Beran58/Ozodraha/ozodraha/ozodraha/tileImages/tile_cross.png

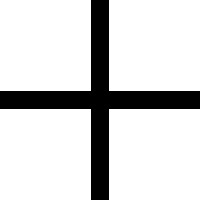
ozodraha/ozodraha/tileImages/tile_cross.png
