Beran58/Ozodraha/ozodraha/ozodraha/tileImages/tile_t_cross.png

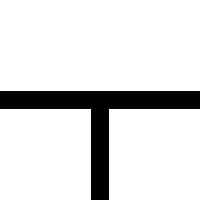
ozodraha/ozodraha/tileImages/tile_t_cross.png
