Beran58/Ozodraha/ozodraha_models/latest_models/slave_module/ozo_platform_v12_bottom.SLDPRT

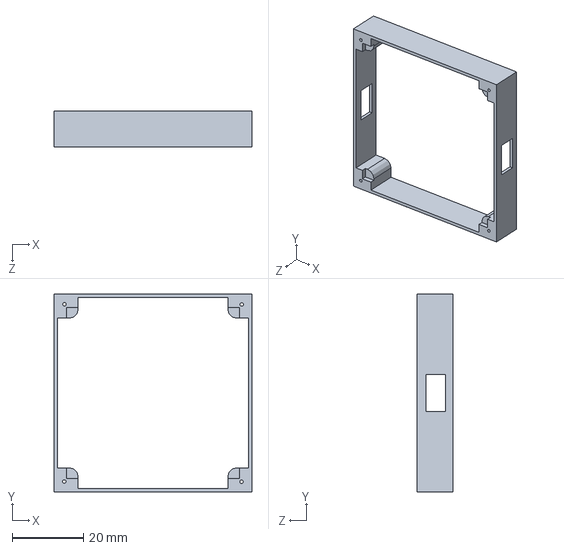
[picture p32: CAD file, 2023-03-25]
ozodraha_models/latest_models/slave_module/ozo_platform_v12_bottom.SLDPRT
55.6 x 55.6 x 10.0 mm
