Beran58/Ozodraha/ozodraha_models/development_models/lines/ozo_line_color_v2.SLDPRT

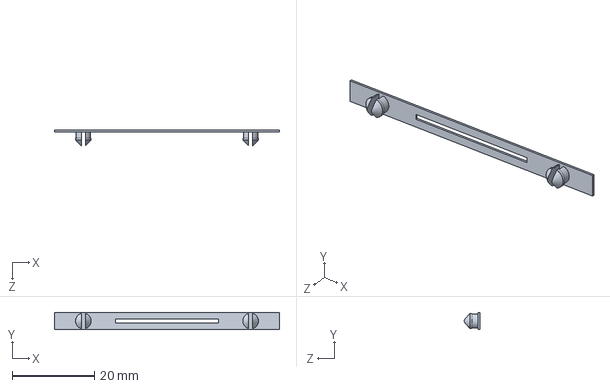
[picture p33: CAD file, 2023-03-25]
ozodraha_models/development_models/lines/ozo_line_color_v2.SLDPRT
54.6 x 4.20 x 3.80 mm
