Beran58/Ozodraha/ozodraha_models/development_models/platforms/ozo_platform_turn.SLDPRT

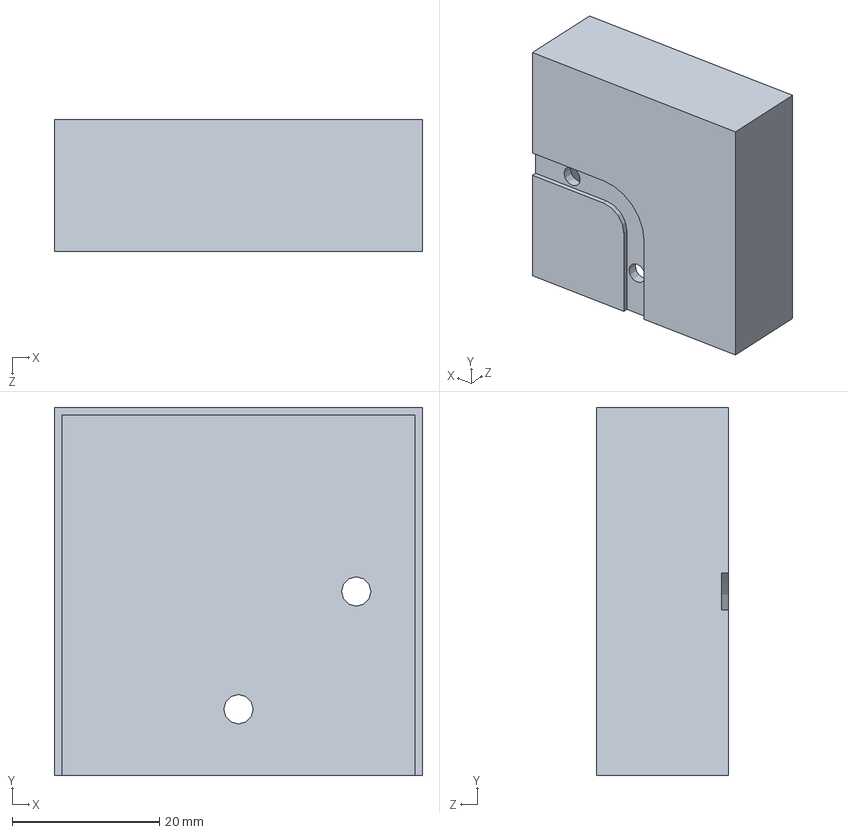
[picture p34: CAD file, 2023-03-25]
ozodraha_models/development_models/platforms/ozo_platform_turn.SLDPRT
50.0 x 50.0 x 18.0 mm
