Beran58/Ozodraha/ozodraha_models/latest_models/lines/ozo_line_cross_v2.SLDPRT

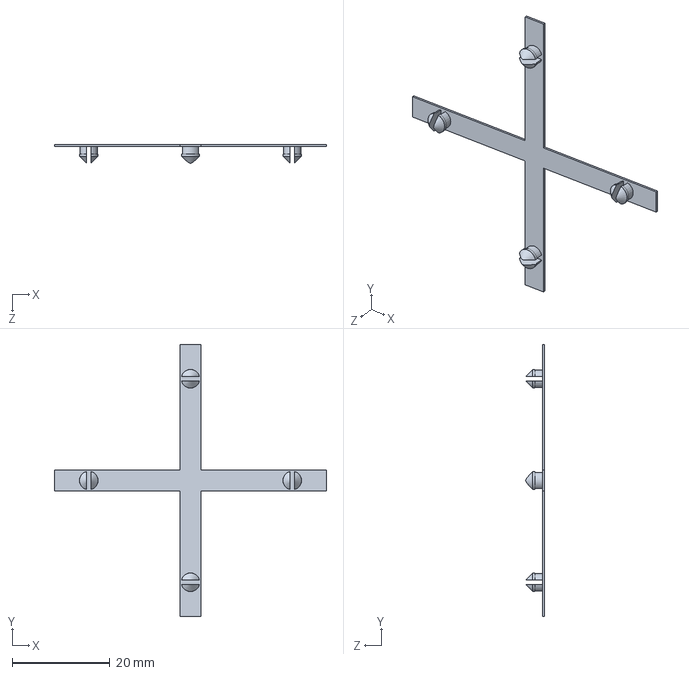
[picture p35: CAD file, 2023-03-25]
ozodraha_models/latest_models/lines/ozo_line_cross_v2.SLDPRT
55.6 x 55.6 x 3.80 mm
