Beran58/Ozodraha/ozodraha_models/latest_models/lines/ozo_line_color_v3.SLDPRT

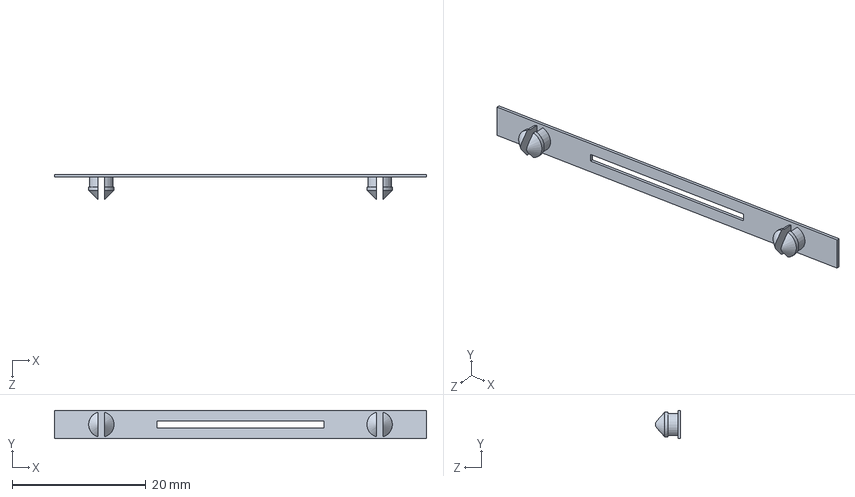
[picture p36: CAD file, 2023-03-25]
ozodraha_models/latest_models/lines/ozo_line_color_v3.SLDPRT
55.6 x 4.20 x 3.80 mm
