Beran58/Ozodraha/ozodraha_models/development_models/lines/ozo_line_turn.SLDPRT

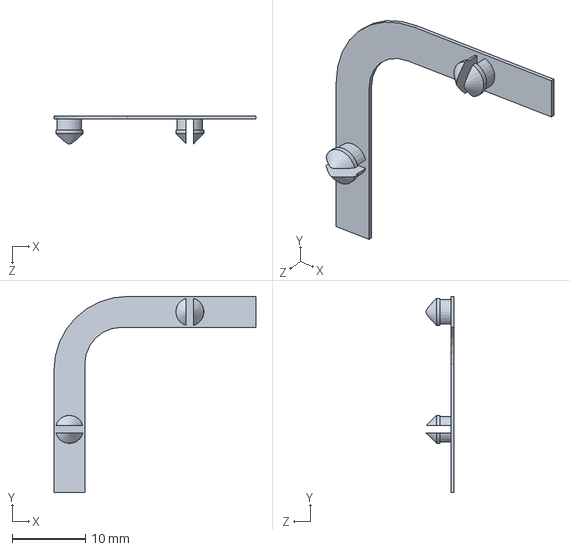
[picture p37: CAD file, 2023-03-25]
ozodraha_models/development_models/lines/ozo_line_turn.SLDPRT
27.5 x 26.7 x 3.80 mm
