Beran58/Ozodraha/ozodraha_models/development_models/lines/ozo_line_60.SLDPRT

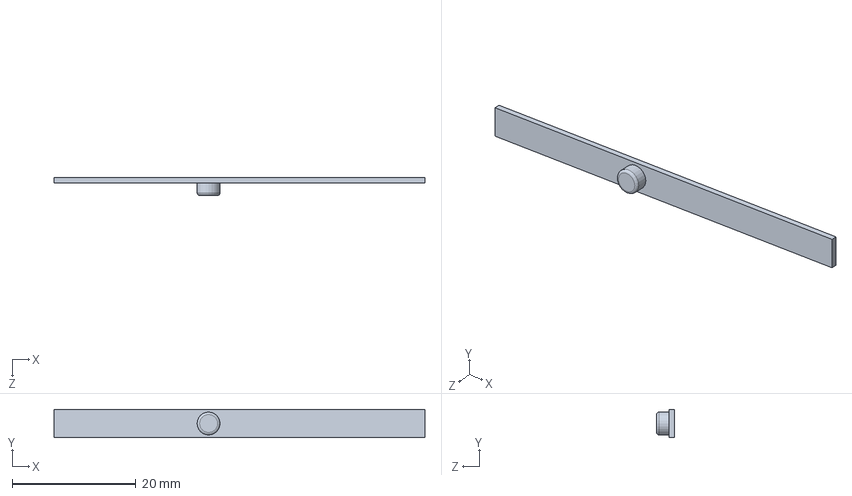
[picture p39: CAD file, 2023-03-25]
ozodraha_models/development_models/lines/ozo_line_60.SLDPRT
60.0 x 4.60 x 2.90 mm
