Beran58/Ozodraha/ozodraha_models/development_models/misc/ozo_diode_holder_v3_Top.SLDPRT

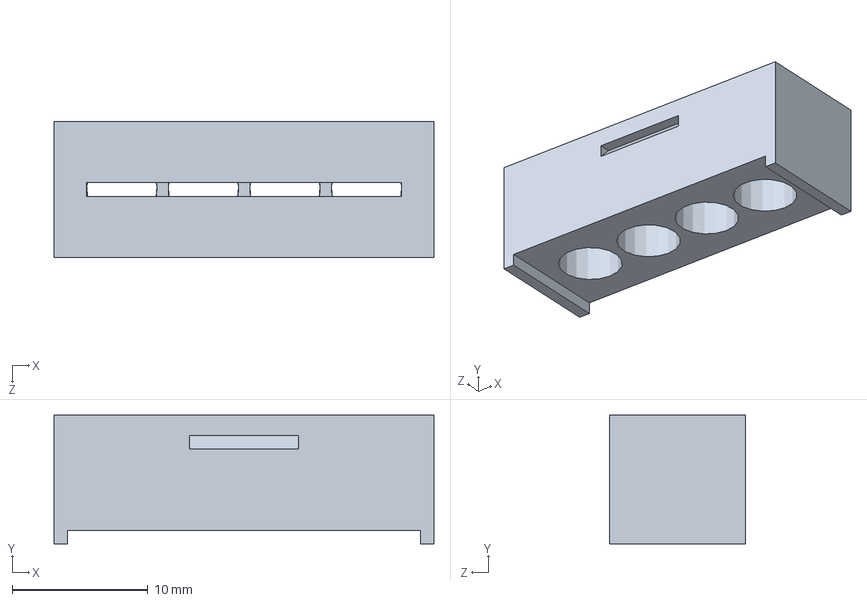
[picture p40: CAD file, 2023-03-25]
ozodraha_models/development_models/misc/ozo_diode_holder_v3_Top.SLDPRT
28.0 x 9.50 x 10.0 mm
