Beran58/Ozodraha/ozodraha_models/development_models/platforms/ozo_platform.SLDPRT

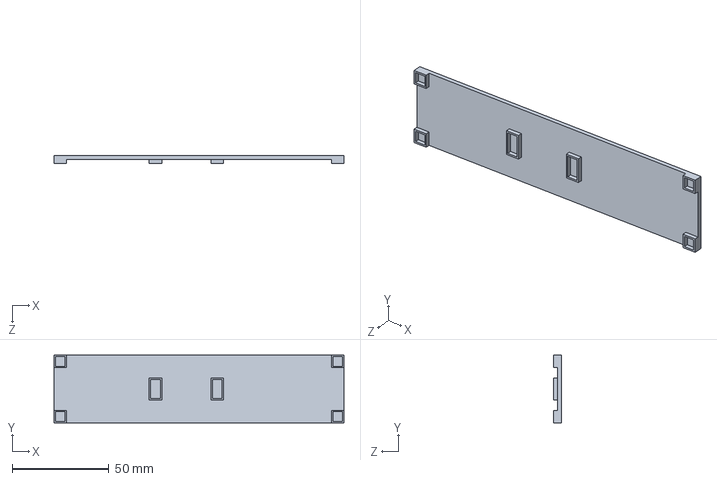
[picture p41: CAD file, 2023-03-25]
ozodraha_models/development_models/platforms/ozo_platform.SLDPRT
150.0 x 35.0 x 4.00 mm
