Beran58/Ozodraha/ozodraha_models/development_models/misc/ozo_diode_holder_v1.SLDPRT

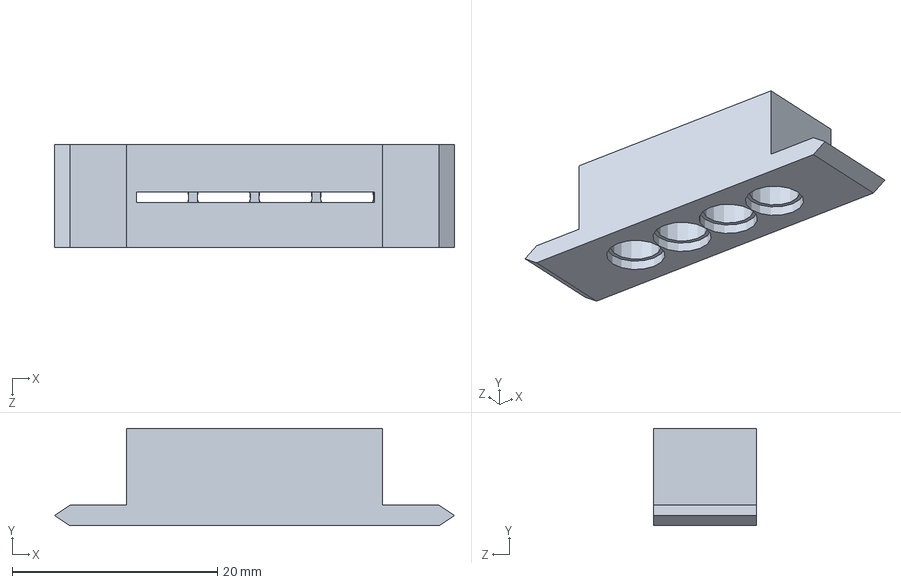
[picture p43: CAD file, 2023-03-25]
ozodraha_models/development_models/misc/ozo_diode_holder_v1.SLDPRT
39.0 x 9.50 x 10.0 mm
