Beran58/Ozodraha/ozodraha_models/development_models/lines/ozo_line.SLDPRT

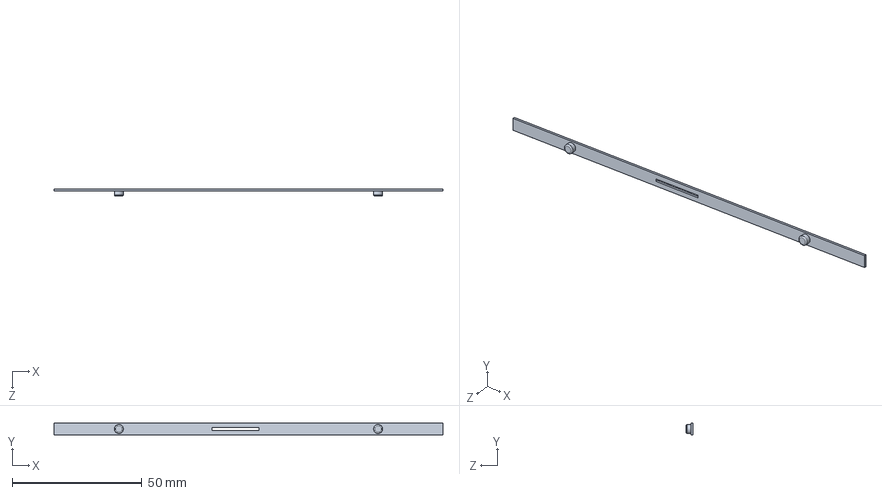
[picture p44: CAD file, 2023-03-25]
ozodraha_models/development_models/lines/ozo_line.SLDPRT
150.0 x 4.60 x 2.80 mm
