Beran58/Ozodraha/ozodraha_models/development_models/lines/ozo_line_T_v1.SLDPRT

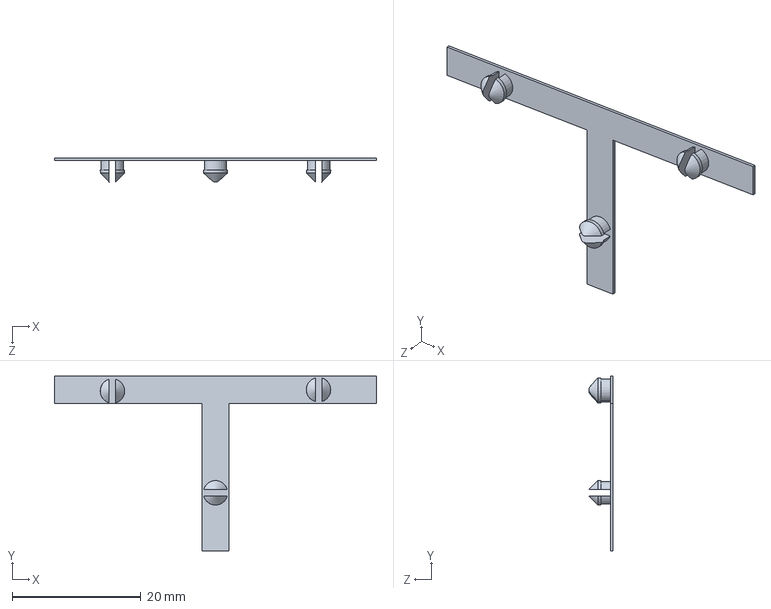
[picture p45: CAD file, 2023-03-25]
ozodraha_models/development_models/lines/ozo_line_T_v1.SLDPRT
50.0 x 27.1 x 3.80 mm
