Beran58/Ozodraha/ozodraha_models/development_models/lines/ozo_line_v3_spaces.SLDPRT

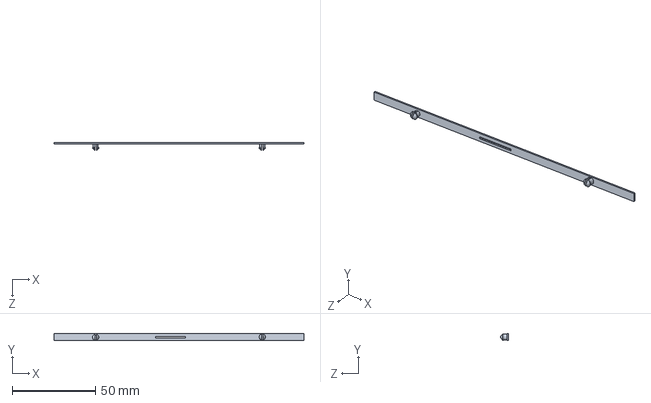
[picture p46: CAD file, 2023-03-25]
ozodraha_models/development_models/lines/ozo_line_v3_spaces.SLDPRT
150.0 x 4.20 x 4.90 mm
