Beran58/Ozodraha/ozodraha_models/development_models/lines/ozo_line_turn_v2.SLDPRT

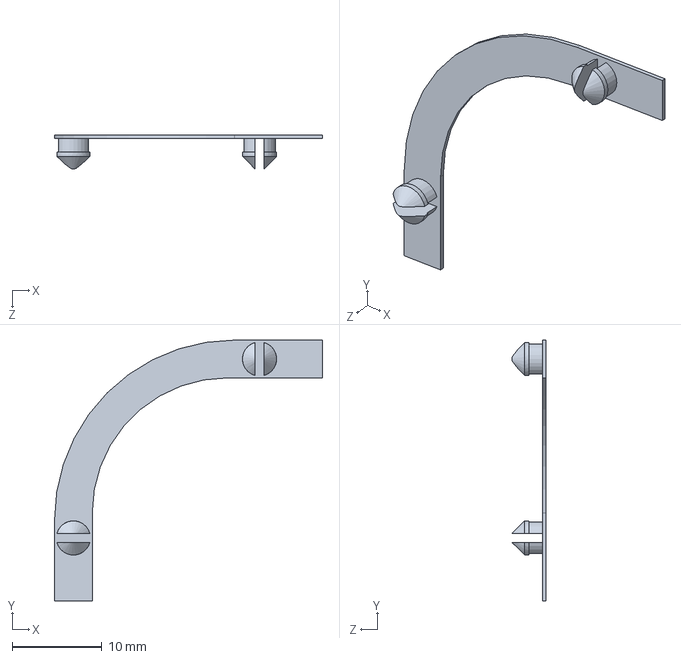
[picture p47: CAD file, 2023-03-25]
ozodraha_models/development_models/lines/ozo_line_turn_v2.SLDPRT
29.8 x 29.0 x 3.80 mm
