Beran58/Ozodraha/ozodraha_models/development_models/slave_module/ozo_platform_v9_bottom_tmp.STL

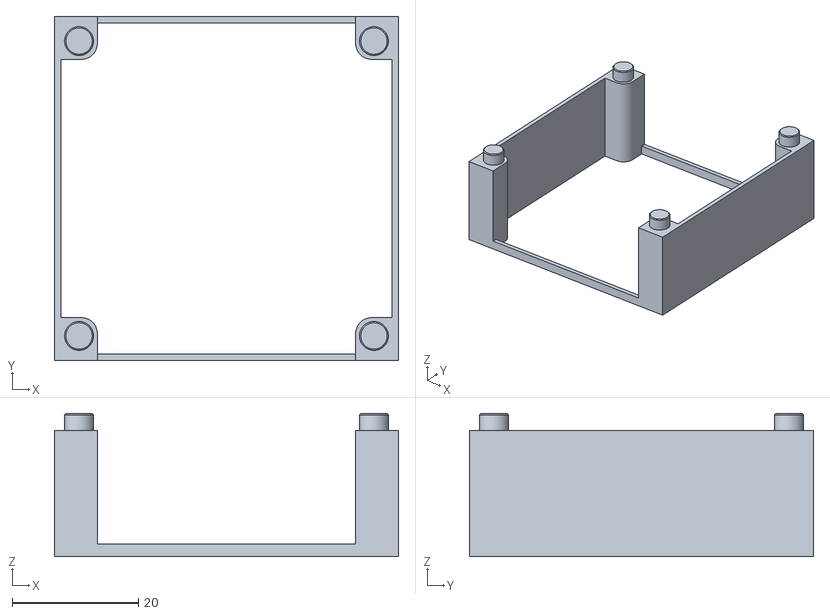
[picture p48: CAD file, 2023-03-25]
ozodraha_models/development_models/slave_module/ozo_platform_v9_bottom_tmp.STL
54.6 x 54.6 x 22.7
