Beran58/Ozodraha/ozodraha_models/development_models/lines/ozo_line_cross_v1.SLDPRT

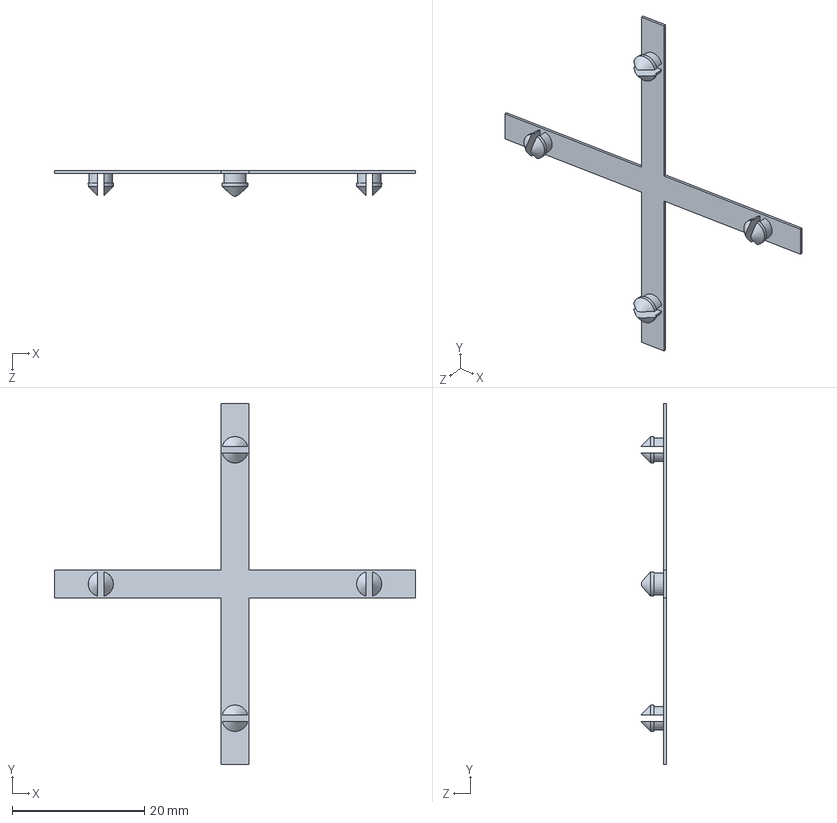
[picture p49: CAD file, 2023-03-25]
ozodraha_models/development_models/lines/ozo_line_cross_v1.SLDPRT
54.6 x 54.6 x 3.90 mm
